brico-labs/BATS/doc/out/bats_pcb.pdf

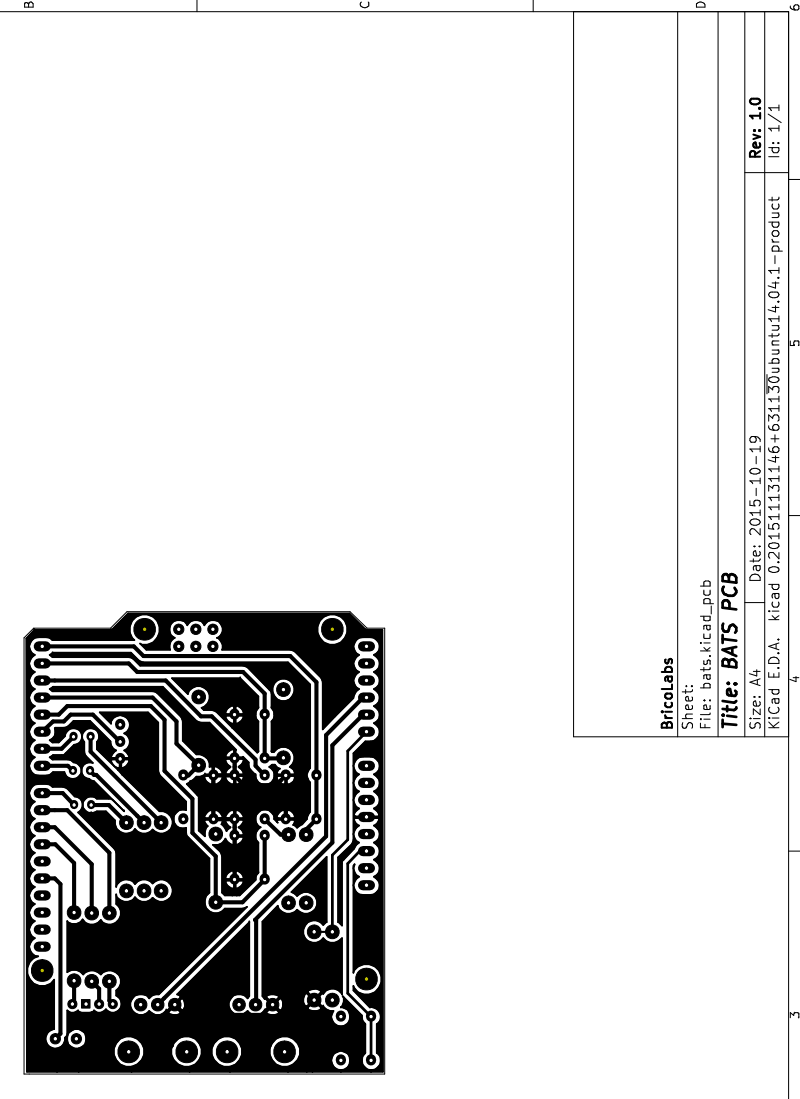
[picture p42: page 1]

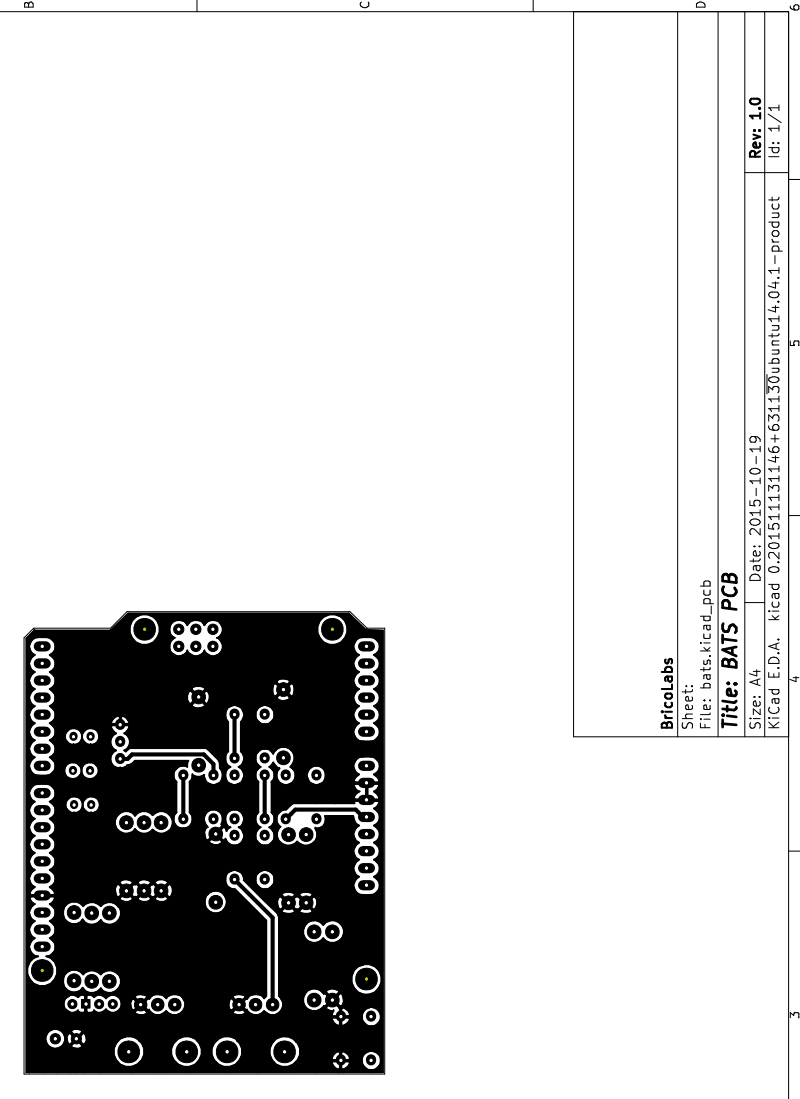
[picture p43: page 2]

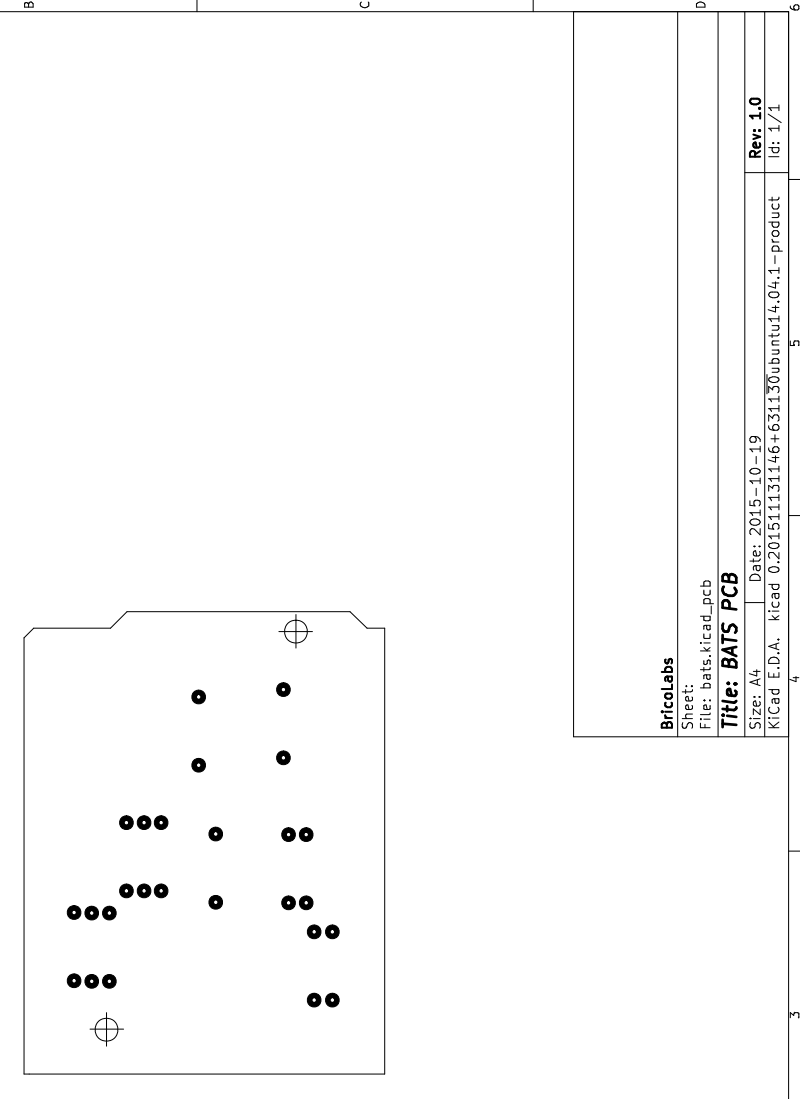
[picture p44: page 3]

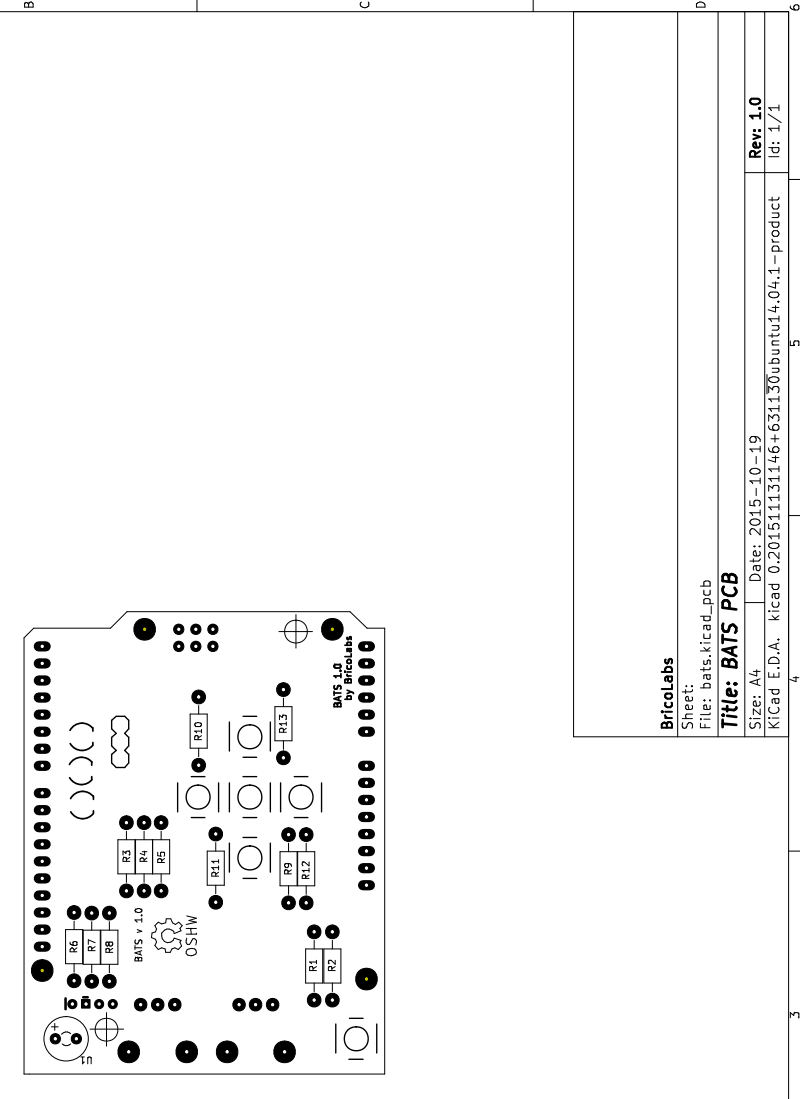
[picture p45: page 4]

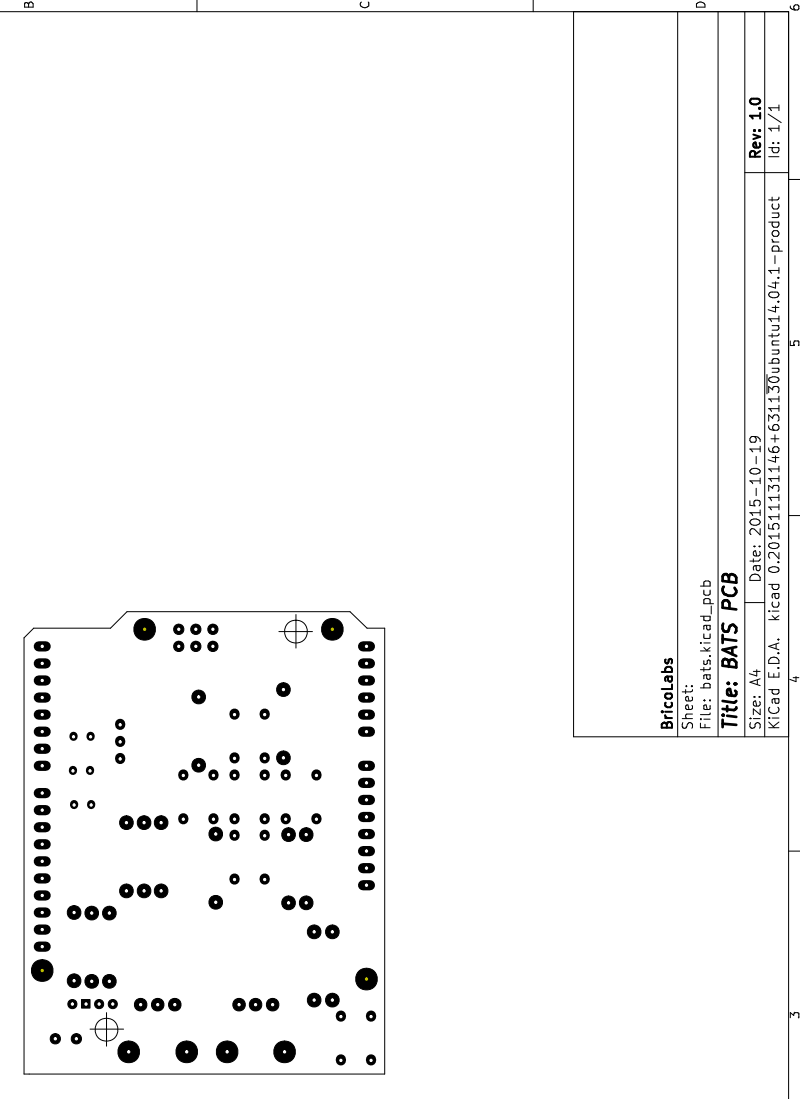
[picture p46: page 5]
