brico-labs/BATS/doc/out/bats_esquema.pdf

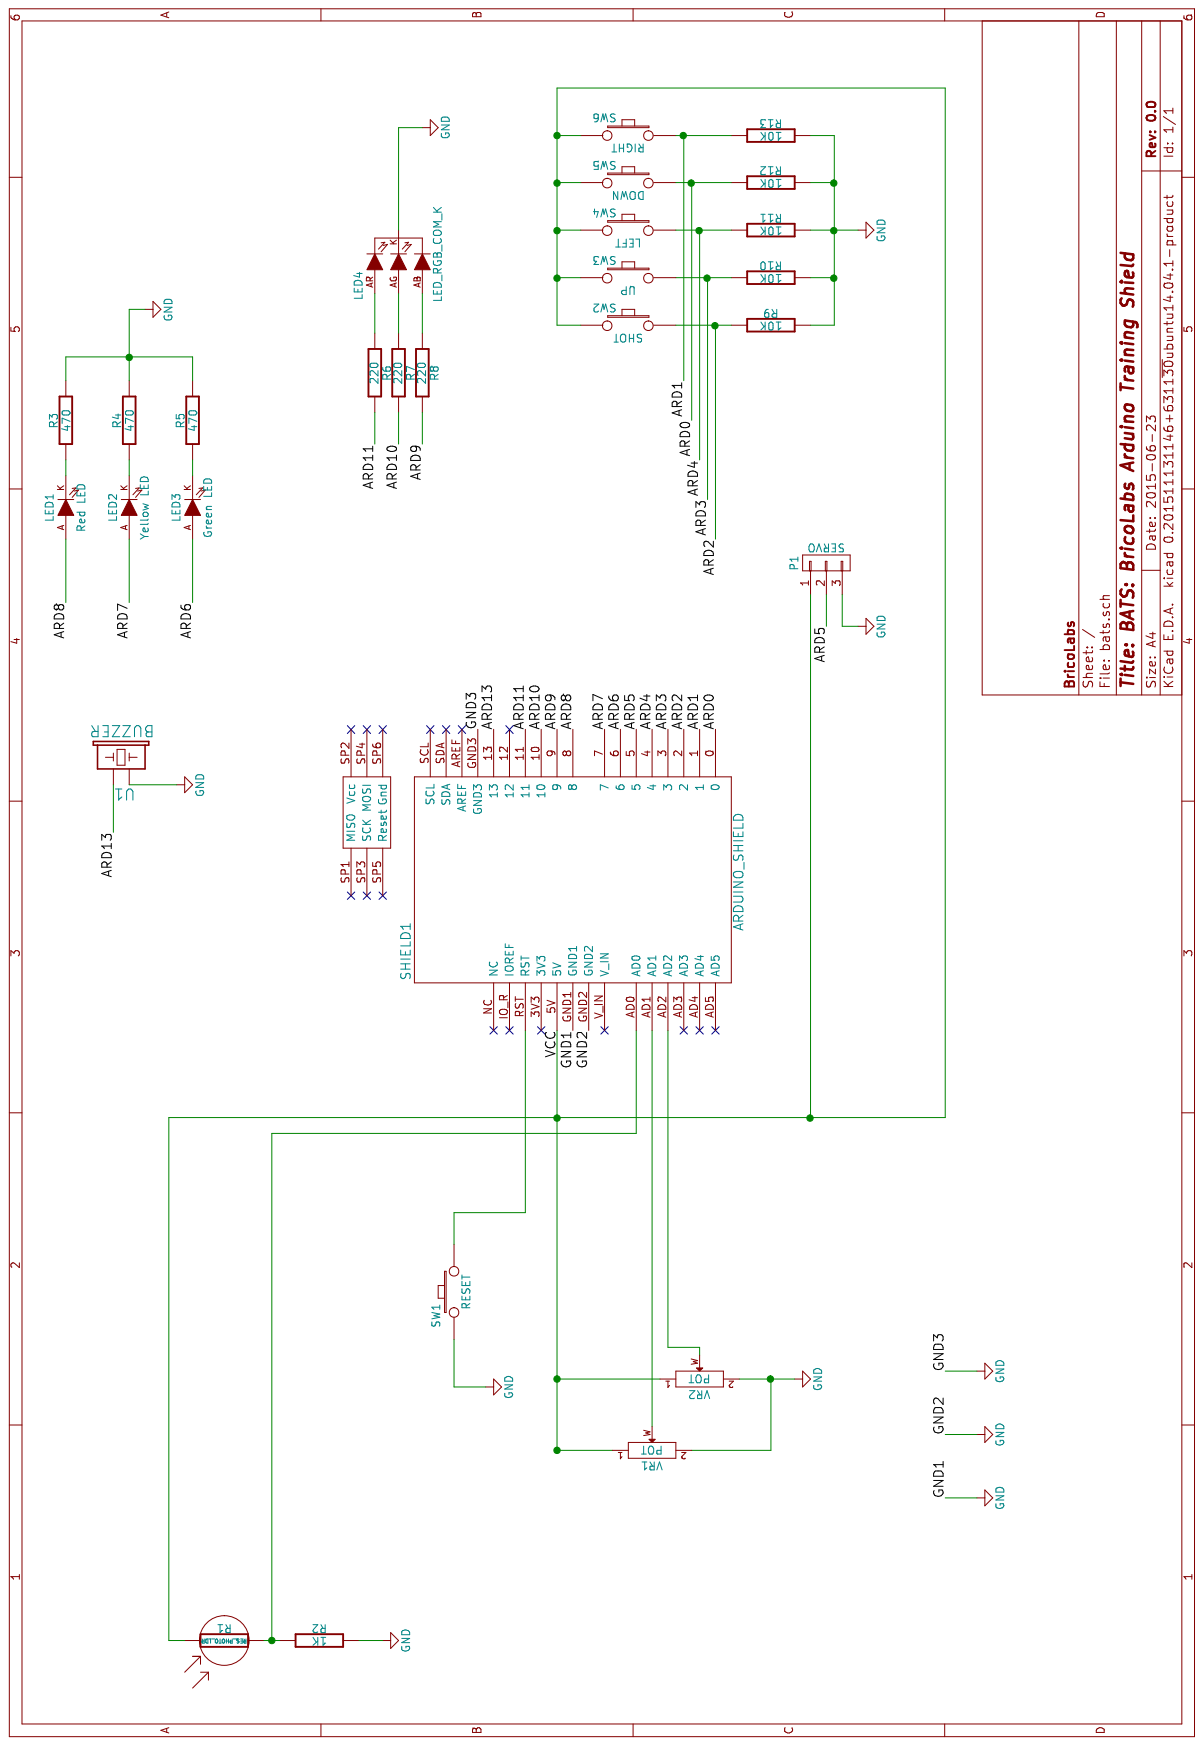
[picture p47: page 1]
