brico-labs/BATS/doc/KiCAD_exports/PCB/exportPDF/bats-B.Cu.pdf

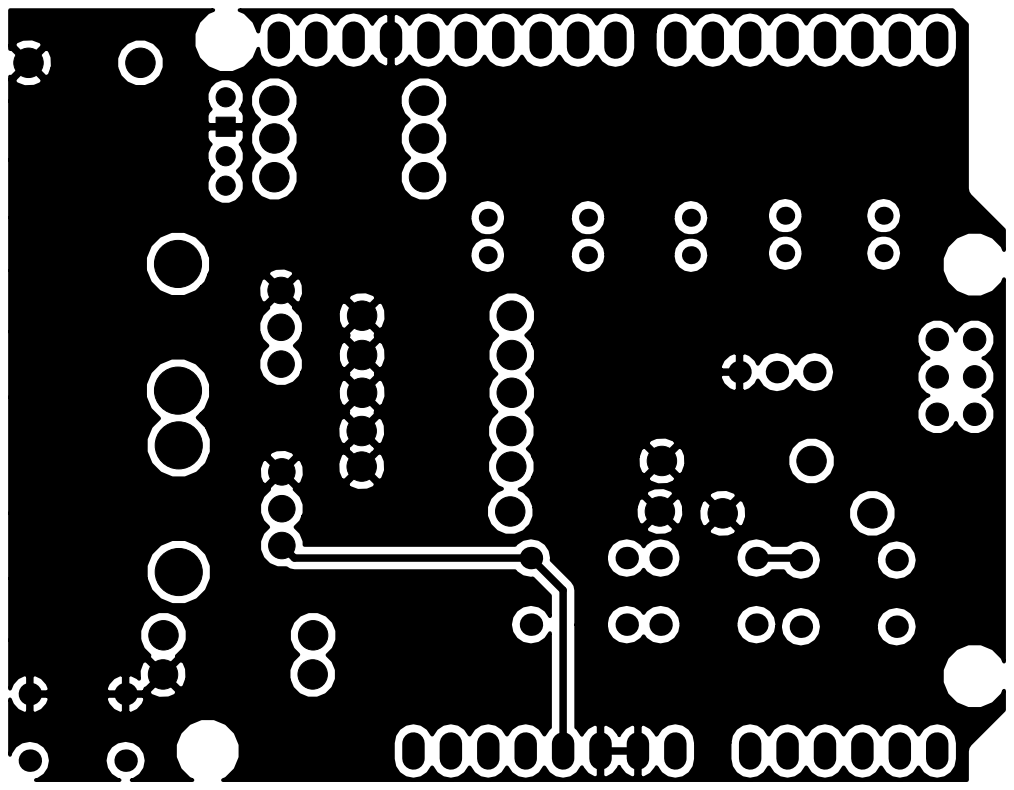
[picture p48: page 1]
