brico-labs/BATS/doc/KiCAD_exports/PCB/exportPDF/bats-B.Mask.pdf

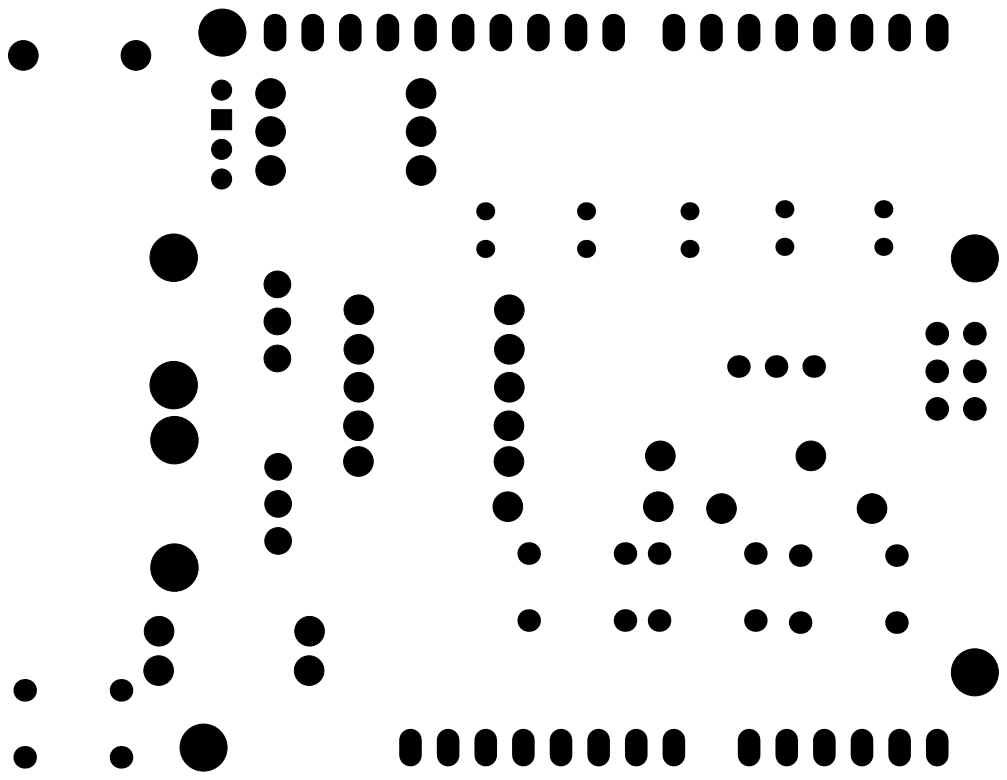
[picture p49: page 1]
