brico-labs/BATS/doc/KiCAD_exports/PCB/exportPDF/bats-B.SilkS.pdf

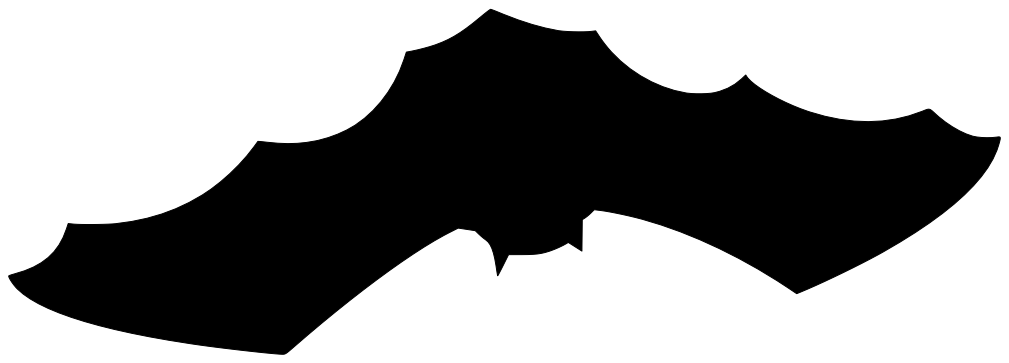
[picture p50: page 1]
