brico-labs/BATS/doc/KiCAD_exports/PCB/exportPDF/bats-F.Cu.pdf

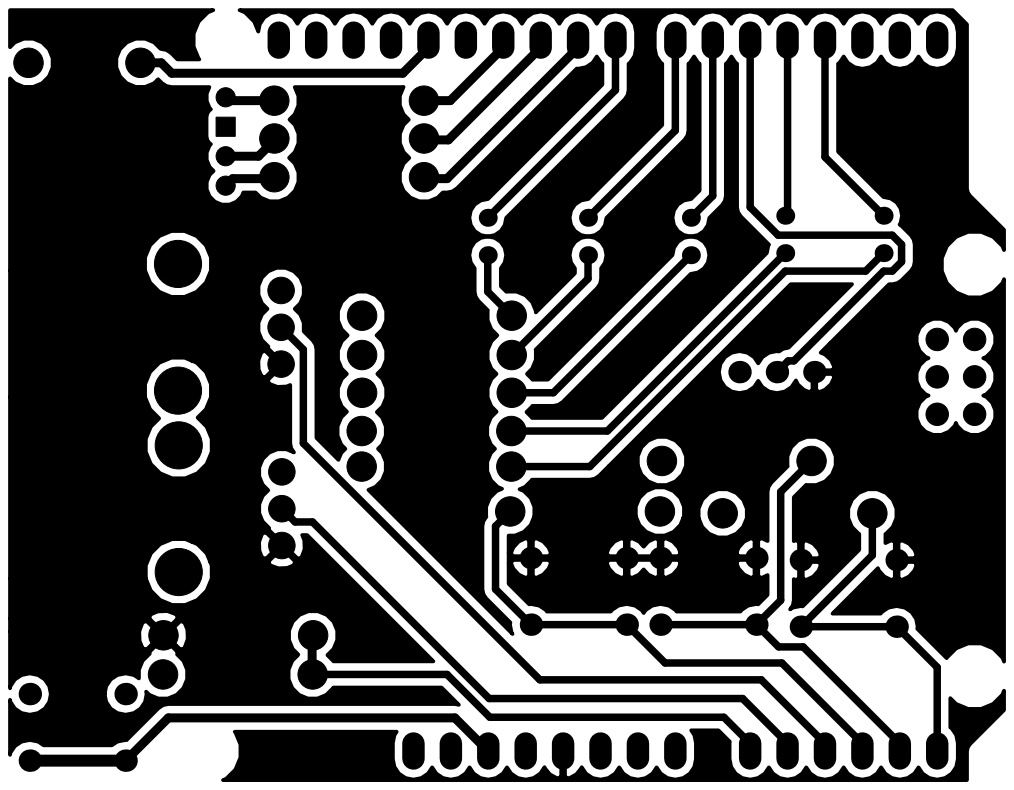
[picture p51: page 1]
