brico-labs/BATS/doc/KiCAD_exports/PCB/exportPDF/bats-F.SilkS.pdf

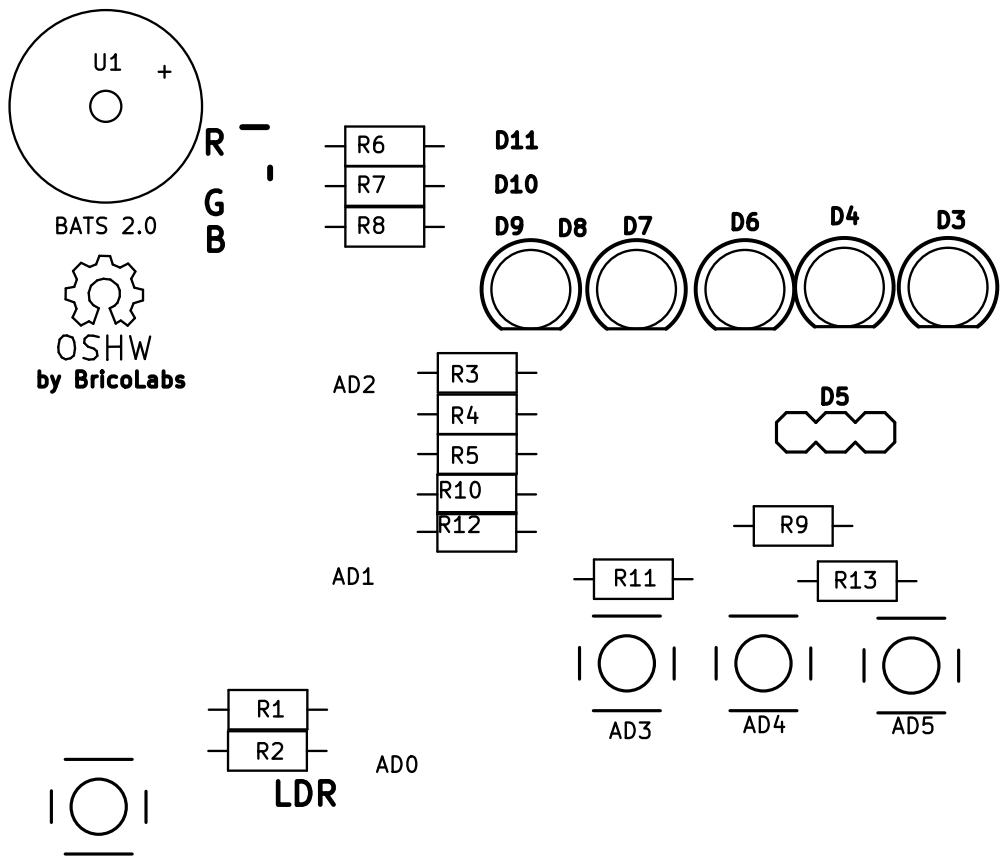
[picture p52: page 1]
