brico-labs/BATS/sw/BATS_vumeter/vumeter.ino

void setup()
{
  pinMode(8,OUTPUT);
  pinMode(7,OUTPUT);
  pinMode(6,OUTPUT);
  pinMode(4,OUTPUT);
  pinMode(3,OUTPUT);
}

void loop()
{
  int a=analogRead(A1);
  if (a>200)
  {
    digitalWrite(8,HIGH);
  }
  else
  {
    analogWrite(8,LOW);
  }
  if (a>400)
  {
    digitalWrite(7,HIGH);
  }
  else
  {
    digitalWrite(7,LOW);
  }
  if (a>600)
  {
    digitalWrite(6,HIGH);
  }
  else
  {
    digitalWrite(6,LOW);
  }
  if (a>800)
  {
    digitalWrite(4,HIGH);
  }
  else
  {
    digitalWrite(4,LOW);
  }
  if (a>1000)
  {
    digitalWrite(3,HIGH);
  }
  else
  {
    digitalWrite(3,LOW);
  }
}
